phaxe82/mp-h1-speaker/images/untitled-90.jpg

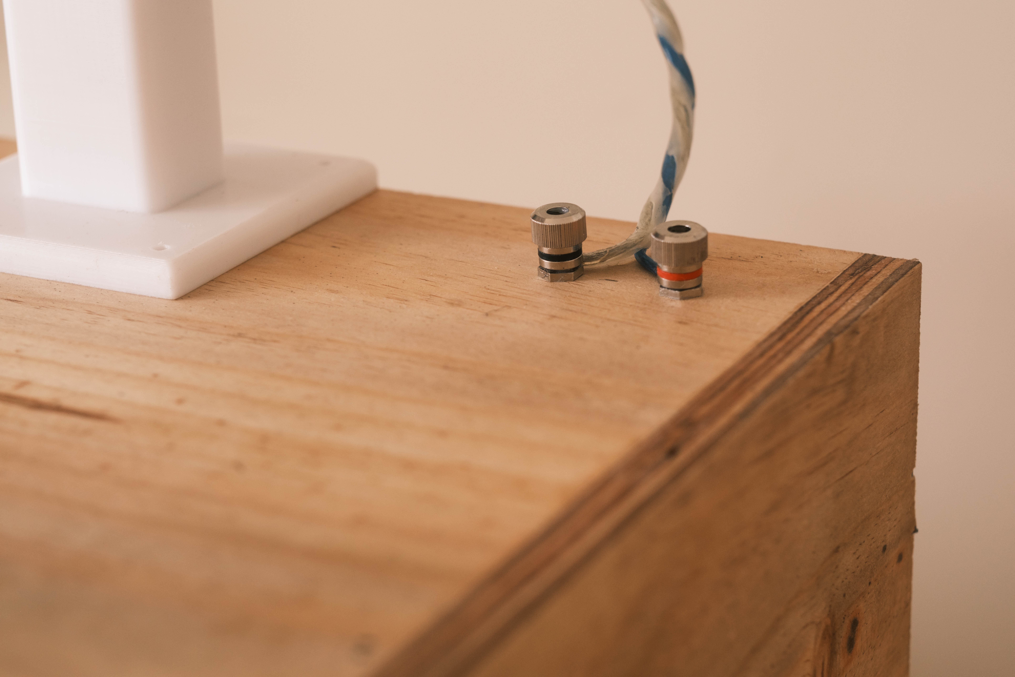
images/untitled-90.jpg
