phaxe82/mp-h1-speaker/images/untitled-99.jpg

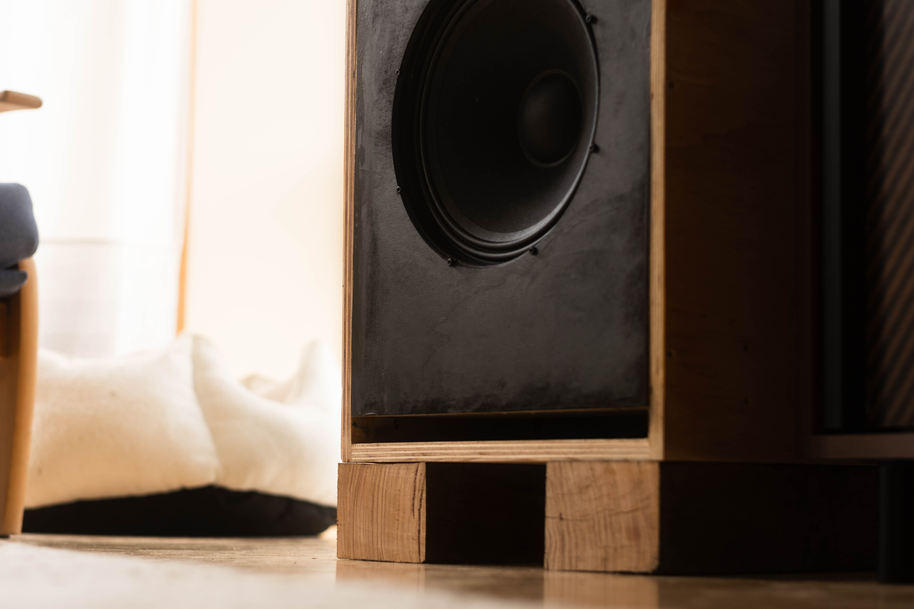
images/untitled-99.jpg
