phaxe82/mp-h1-speaker/images/untitled-105.jpg

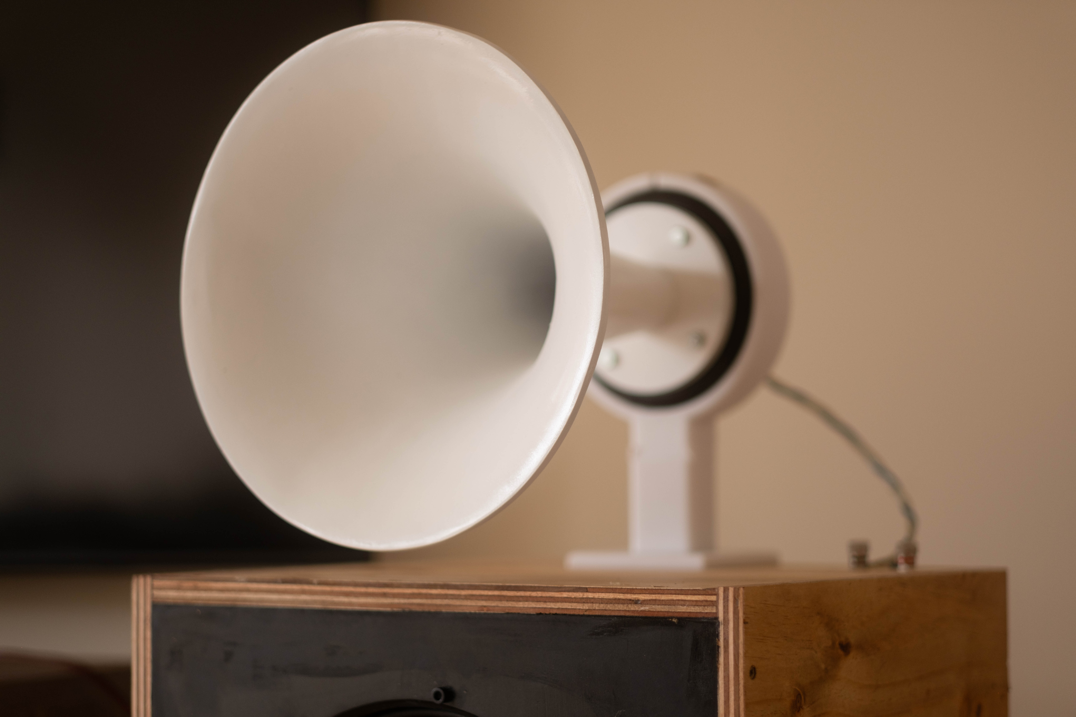
images/untitled-105.jpg
